gurues/CuboMagico/Esquemas/Esquema_Electrico.JPG

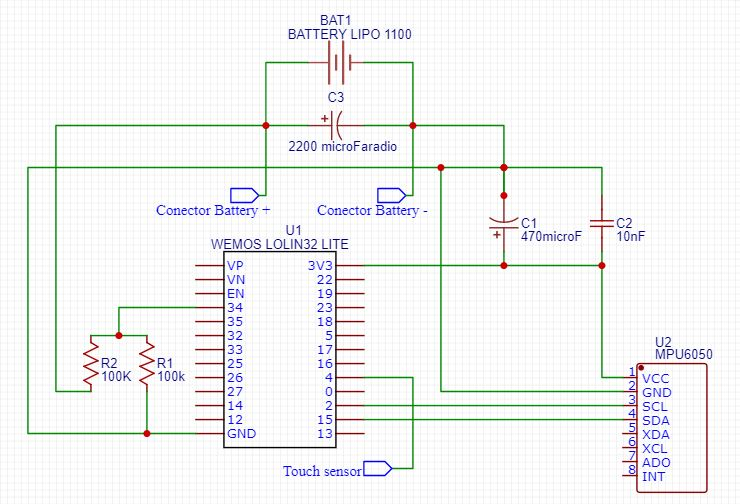
Esquemas/Esquema_Electrico.JPG
