gurues/CuboMagico/Foto-Video/05_Cubo.jpg

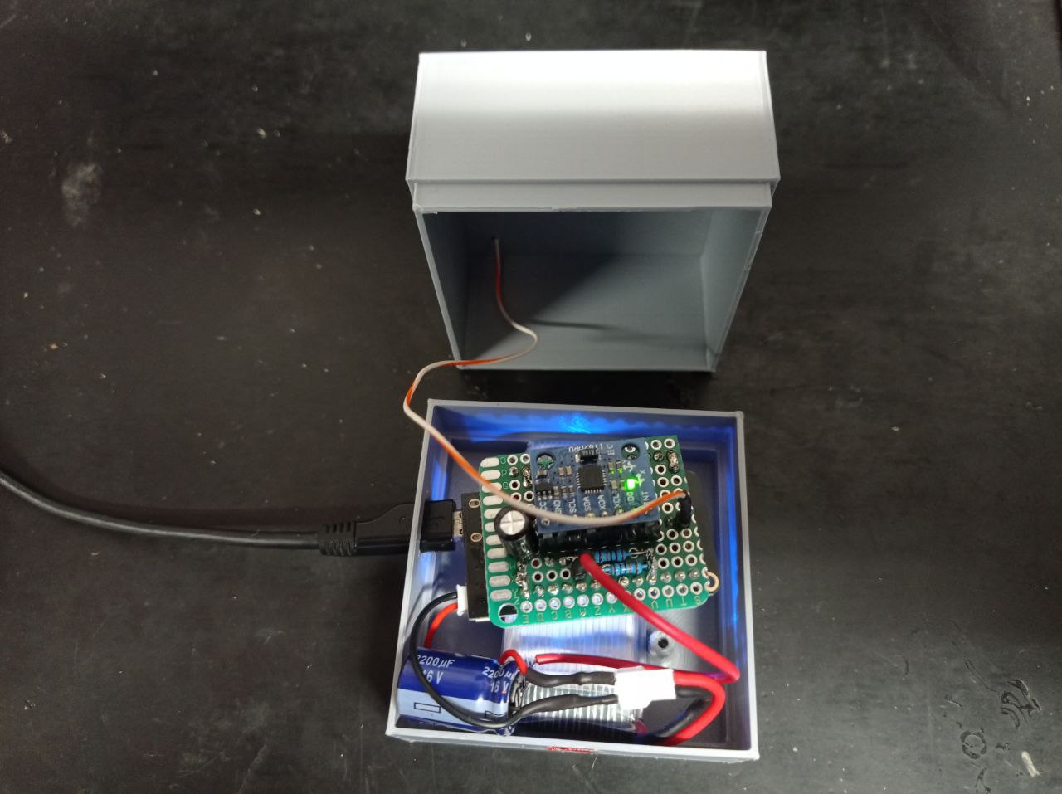
Foto-Video/05_Cubo.jpg
