gurues/CuboMagico/Foto-Video/06_Cubo.jpg

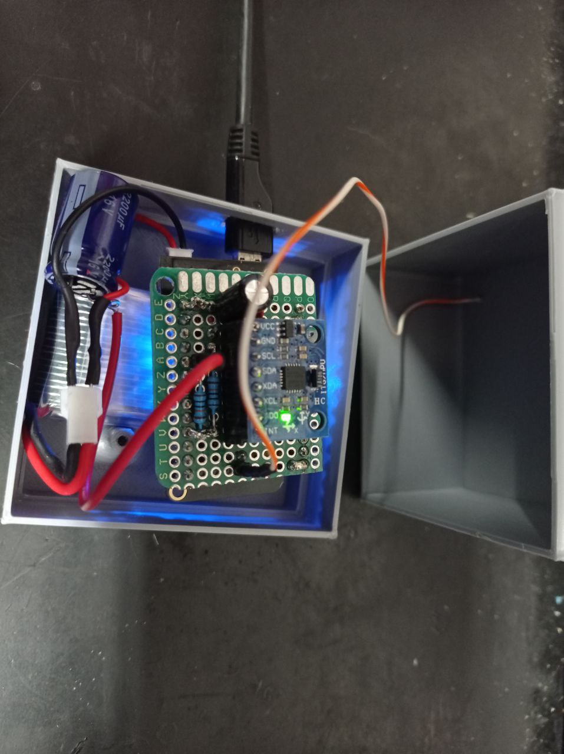
Foto-Video/06_Cubo.jpg
